sz24sz24-5607/birdy-project/mechanic/box_bottom.stl

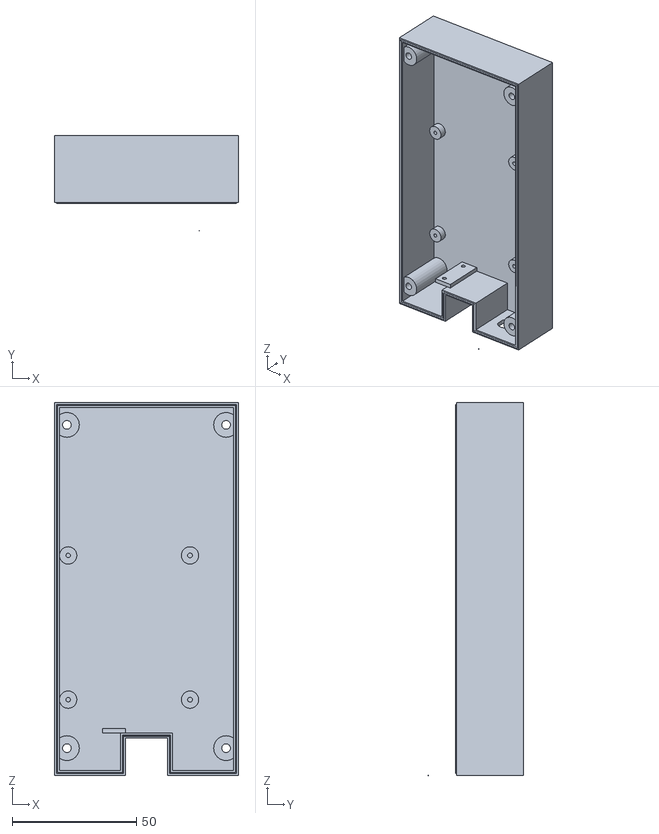
[picture p20: CAD file, 2026-02-25]
mechanic/box_bottom.stl
74.0 x 38.4 x 150.0
