sz24sz24-5607/birdy-project/mechanic/feeder_plate.stl

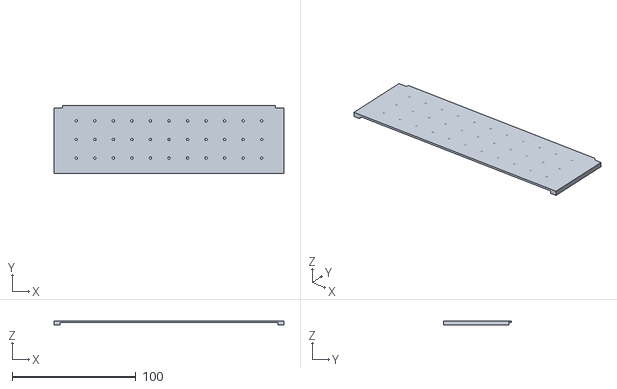
[picture p21: CAD file, 2026-02-25]
mechanic/feeder_plate.stl
186.0 x 55.0 x 3.50
