sz24sz24-5607/birdy-project/birdy_config/asgi.py

"""
ASGI config for birdy_config project.

It exposes the ASGI callable as a module-level variable named ``application``.

For more information on this file, see
https://docs.djangoproject.com/en/5.0/howto/deployment/asgi/
"""

import os

from django.core.asgi import get_asgi_application

os.environ.setdefault('DJANGO_SETTINGS_MODULE', 'birdy_config.settings')

application = get_asgi_application()
