sz24sz24-5607/birdy-project/birdy_config/wsgi.py

"""
WSGI config for birdy_config project.

It exposes the WSGI callable as a module-level variable named ``application``.

For more information on this file, see
https://docs.djangoproject.com/en/5.0/howto/deployment/wsgi/
"""

import os

from django.core.wsgi import get_wsgi_application

os.environ.setdefault('DJANGO_SETTINGS_MODULE', 'birdy_config.settings')

application = get_wsgi_application()
